timdrysdale/box-power/doc/Design Guide - PMOS MOSFET for Reverse Voltage Polarity Protection Circuit_files/board-mount-AC-DC-converters-RECOM.jpg

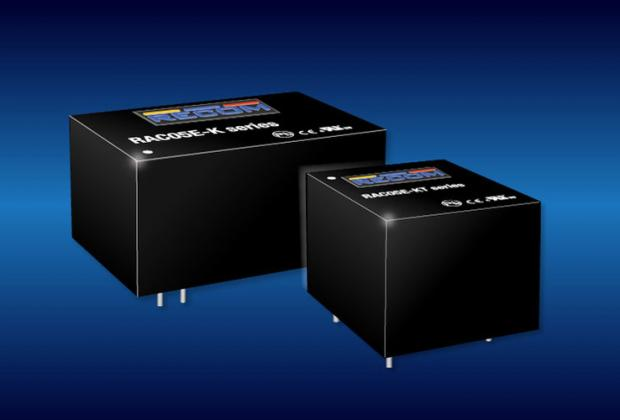
doc/Design Guide - PMOS MOSFET for Reverse Voltage Polarity Protection Circuit_files/board-mount-AC-DC-converters-RECOM.jpg
