timdrysdale/box-power/doc/Design Guide - PMOS MOSFET for Reverse Voltage Polarity Protection Circuit_files/AOTL66810-80V-Power-MOSFET.jpg

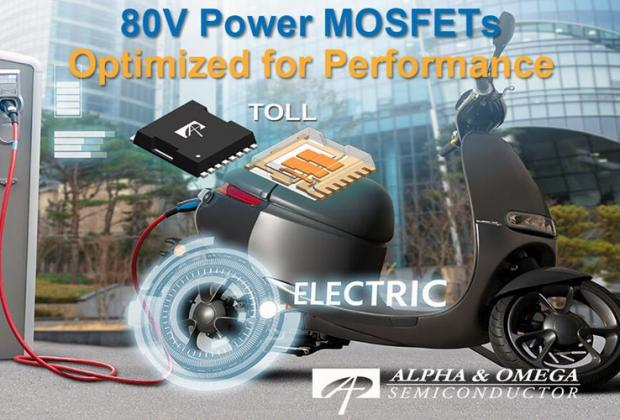
doc/Design Guide - PMOS MOSFET for Reverse Voltage Polarity Protection Circuit_files/AOTL66810-80V-Power-MOSFET.jpg
