timdrysdale/box-power/doc/Reverse Polarity Protection – Electronic Product Design_files/reverse_polarity_protect_24v.png

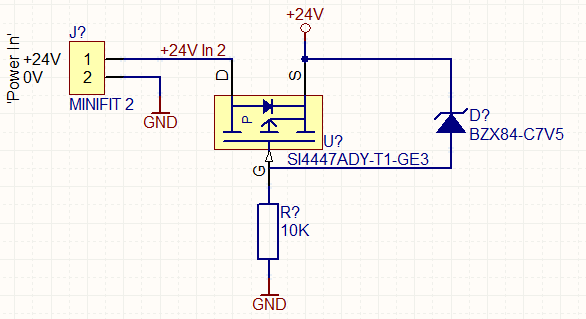
doc/Reverse Polarity Protection – Electronic Product Design_files/reverse_polarity_protect_24v.png
