timdrysdale/box-power/img/Screenshot from 2021-11-20 15-01-30.png

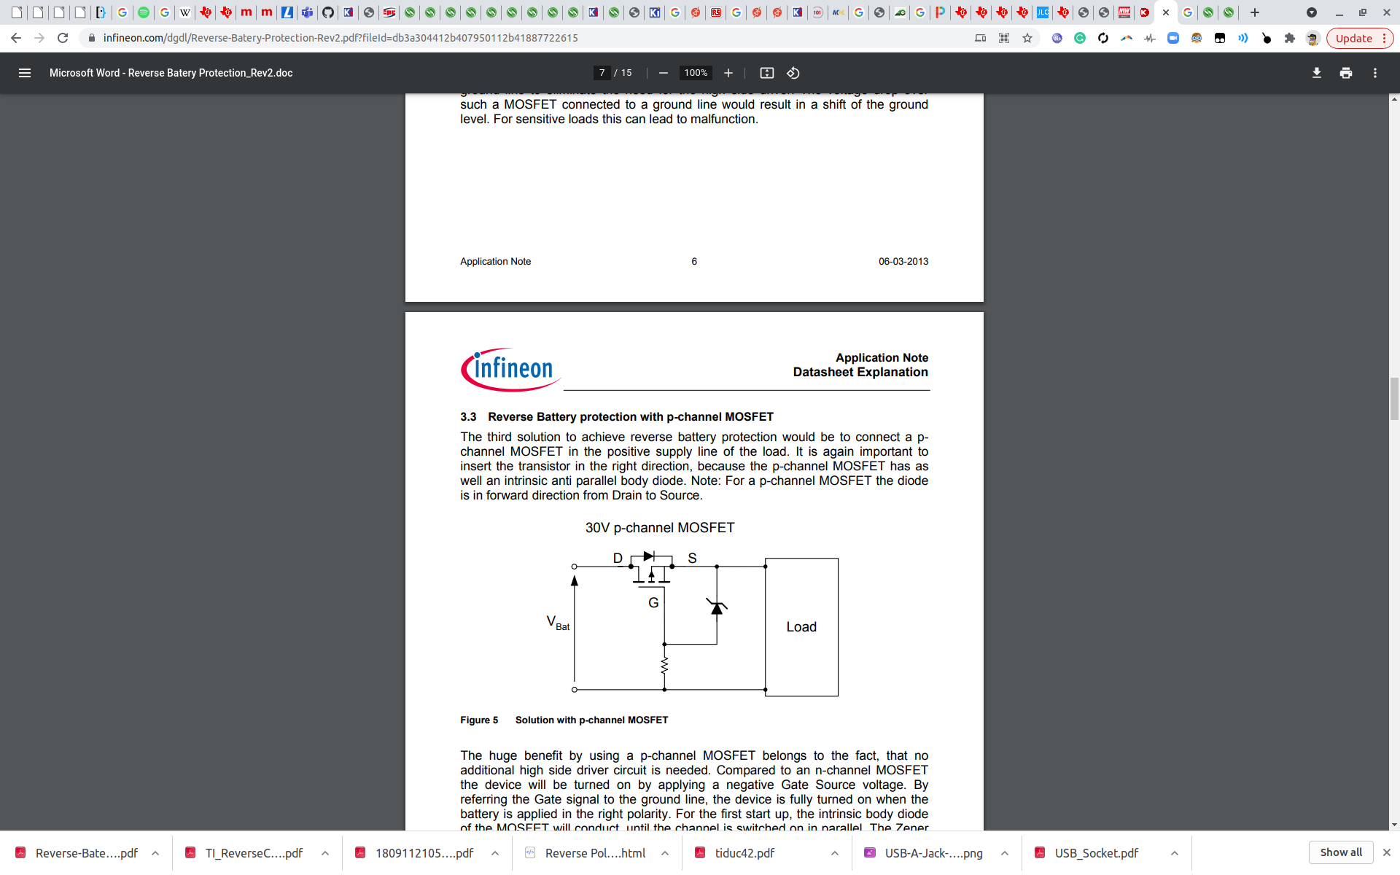
img/Screenshot from 2021-11-20 15-01-30.png
