timdrysdale/box-power/pcb/single/single.png

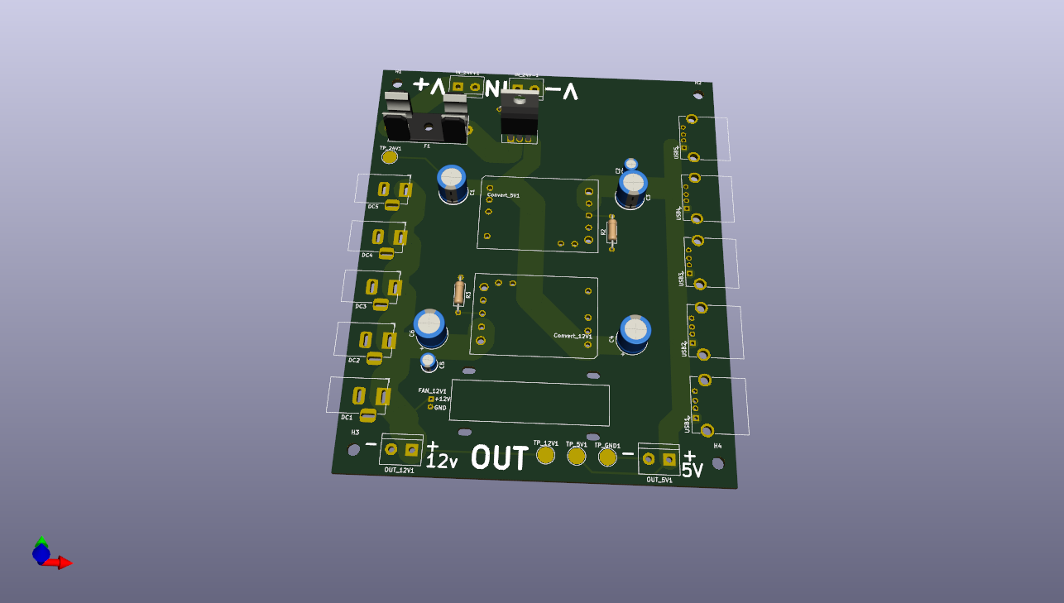
pcb/single/single.png
