timdrysdale/box-power/doc/Design Guide - PMOS MOSFET for Reverse Voltage Polarity Protection Circuit_files/300x250-1.gif

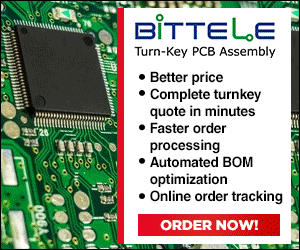
doc/Design Guide - PMOS MOSFET for Reverse Voltage Polarity Protection Circuit_files/300x250-1.gif
