timdrysdale/box-power/doc/Design Guide - PMOS MOSFET for Reverse Voltage Polarity Protection Circuit_files/BME280-Sensor.jpg

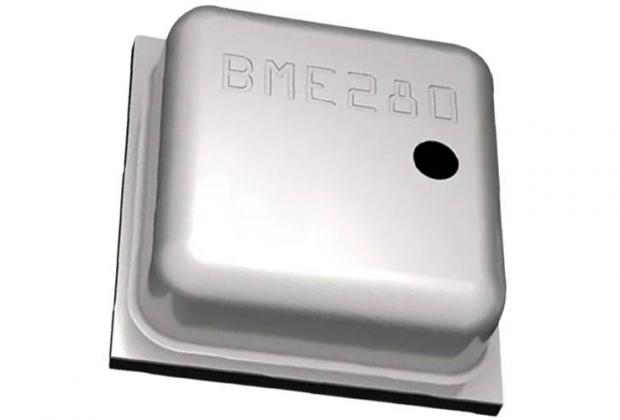
doc/Design Guide - PMOS MOSFET for Reverse Voltage Polarity Protection Circuit_files/BME280-Sensor.jpg
