timdrysdale/box-power/doc/Design Guide - PMOS MOSFET for Reverse Voltage Polarity Protection Circuit_files/Orcad-PSPICE-Circuit-Simulation.jpg

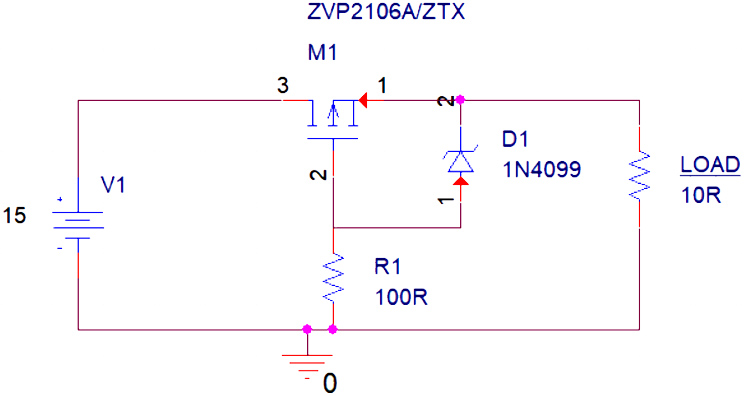
doc/Design Guide - PMOS MOSFET for Reverse Voltage Polarity Protection Circuit_files/Orcad-PSPICE-Circuit-Simulation.jpg
