timdrysdale/box-power/doc/Design Guide - PMOS MOSFET for Reverse Voltage Polarity Protection Circuit_files/PMOS-Reverse-Polarity-Protection-Circuit.png

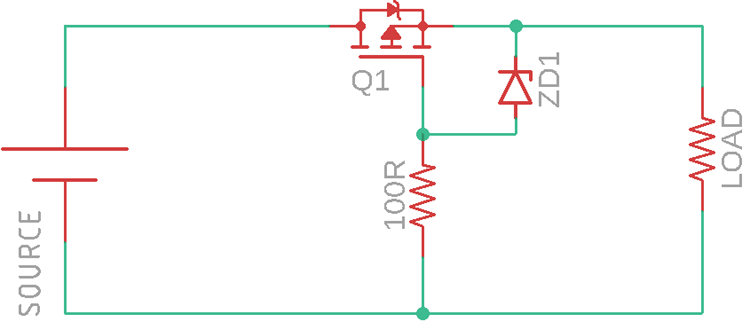
doc/Design Guide - PMOS MOSFET for Reverse Voltage Polarity Protection Circuit_files/PMOS-Reverse-Polarity-Protection-Circuit.png
