timdrysdale/box-power/doc/Design Guide - PMOS MOSFET for Reverse Voltage Polarity Protection Circuit_files/Reverse-Voltage-Polarity-Protection-circuit.png

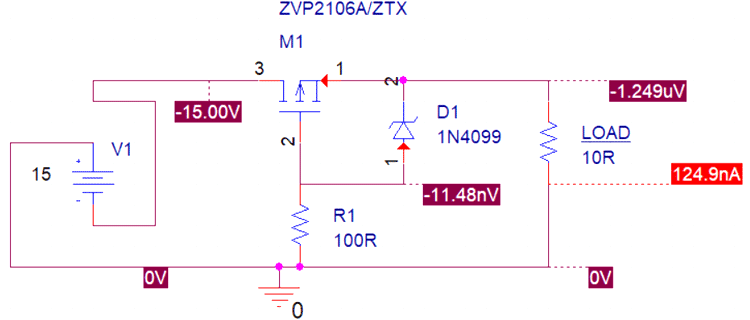
doc/Design Guide - PMOS MOSFET for Reverse Voltage Polarity Protection Circuit_files/Reverse-Voltage-Polarity-Protection-circuit.png
